bikerglen/usb-knob-box-bmd-remote/pic18/software/USB-Knobs-v02.X/system.c

/*******************************************************************************
Copyright 2016 Microchip Technology Inc. (www.microchip.com)

Licensed under the Apache License, Version 2.0 (the "License");
you may not use this file except in compliance with the License.
You may obtain a copy of the License at

    http://www.apache.org/licenses/LICENSE-2.0

Unless required by applicable law or agreed to in writing, software
distributed under the License is distributed on an "AS IS" BASIS,
WITHOUT WARRANTIES OR CONDITIONS OF ANY KIND, either express or implied.
See the License for the specific language governing permissions and
limitations under the License.

To request to license the code under the MLA license (www.microchip.com/mla_license), 
please contact mla_licensing@microchip.com
*******************************************************************************/

#include <xc.h>
#include "system.h"
#include "usb.h"

/** CONFIGURATION Bits **********************************************/
#pragma config PLLSEL   = PLL3X     // PLL Selection (3x clock multiplier)
#pragma config CFGPLLEN = OFF       // PLL Enable Configuration bit (PLL Disabled (firmware controlled))
#pragma config CPUDIV   = NOCLKDIV  // CPU System Clock Postscaler (CPU uses system clock (no divide))
#pragma config LS48MHZ  = SYS48X8   // Low Speed USB mode with 48 MHz system clock (System clock at 48 MHz, USB clock divider is set to 8)
#pragma config FOSC     = INTOSCIO  // Oscillator Selection (Internal oscillator)
#pragma config PCLKEN   = OFF       // Primary Oscillator Shutdown (Primary oscillator shutdown firmware controlled)
#pragma config FCMEN    = OFF       // Fail-Safe Clock Monitor (Fail-Safe Clock Monitor disabled)
#pragma config IESO     = OFF       // Internal/External Oscillator Switchover (Oscillator Switchover mode disabled)
#pragma config nPWRTEN  = OFF       // Power-up Timer Enable (Power up timer disabled)
#pragma config BOREN    = SBORDIS   // Brown-out Reset Enable (BOR enabled in hardware (SBOREN is ignored))
#pragma config BORV     = 190       // Brown-out Reset Voltage (BOR set to 1.9V nominal)
#pragma config nLPBOR   = ON        // Low-Power Brown-out Reset (Low-Power Brown-out Reset enabled)
#pragma config WDTEN    = SWON      // Watchdog Timer Enable bits (WDT controlled by firmware (SWDTEN enabled))
#pragma config WDTPS    = 32768     // Watchdog Timer Postscaler (1:32768)
#pragma config CCP2MX   = RC1       // CCP2 MUX bit (CCP2 input/output is multiplexed with RC1)
#pragma config PBADEN   = OFF       // PORTB A/D Enable bit (PORTB<5:0> pins are configured as digital I/O on Reset)
#pragma config T3CMX    = RC0       // Timer3 Clock Input MUX bit (T3CKI function is on RC0)
#pragma config SDOMX    = RC7       // SDO Output MUX bit (SDO function is on RC7)
#pragma config MCLRE    = ON        // Master Clear Reset Pin Enable (MCLR pin enabled; RE3 input disabled)
#pragma config STVREN   = ON        // Stack Full/Underflow Reset (Stack full/underflow will cause Reset)
#pragma config LVP      = OFF       // Single-Supply ICSP Enable bit (Single-Supply ICSP disabled)
#pragma config ICPRT    = OFF       // Dedicated In-Circuit Debug/Programming Port Enable (ICPORT disabled)
#pragma config XINST    = OFF       // Extended Instruction Set Enable bit (Instruction set extension and Indexed Addressing mode disabled)
#pragma config CP0      = OFF       // Block 0 Code Protect (Block 0 is not code-protected)
#pragma config CP1      = OFF       // Block 1 Code Protect (Block 1 is not code-protected)
#pragma config CP2      = OFF       // Block 2 Code Protect (Block 2 is not code-protected)
#pragma config CP3      = OFF       // Block 3 Code Protect (Block 3 is not code-protected)
#pragma config CPB      = OFF       // Boot Block Code Protect (Boot block is not code-protected)
#pragma config CPD      = OFF       // Data EEPROM Code Protect (Data EEPROM is not code-protected)
#pragma config WRT0     = OFF       // Block 0 Write Protect (Block 0 (0800-1FFFh) is not write-protected)
#pragma config WRT1     = OFF       // Block 1 Write Protect (Block 1 (2000-3FFFh) is not write-protected)
#pragma config WRT2     = OFF       // Block 2 Write Protect (Block 2 (04000-5FFFh) is not write-protected)
#pragma config WRT3     = OFF       // Block 3 Write Protect (Block 3 (06000-7FFFh) is not write-protected)
#pragma config WRTC     = OFF       // Configuration Registers Write Protect (Configuration registers (300000-3000FFh) are not write-protected)
#pragma config WRTB     = OFF       // Boot Block Write Protect (Boot block (0000-7FFh) is not write-protected)
#pragma config WRTD     = OFF       // Data EEPROM Write Protect (Data EEPROM is not write-protected)
#pragma config EBTR0    = OFF       // Block 0 Table Read Protect (Block 0 is not protected from table reads executed in other blocks)
#pragma config EBTR1    = OFF       // Block 1 Table Read Protect (Block 1 is not protected from table reads executed in other blocks)
#pragma config EBTR2    = OFF       // Block 2 Table Read Protect (Block 2 is not protected from table reads executed in other blocks)
#pragma config EBTR3    = OFF       // Block 3 Table Read Protect (Block 3 is not protected from table reads executed in other blocks)
#pragma config EBTRB    = OFF       // Boot Block Table Read Protect (Boot block is not protected from table reads executed in other blocks)


// S.BUS data
extern volatile uint8_t txByte;
extern volatile uint8_t sbusData[25];

// S>BUS data IRQ parity calculation variables
static uint8_t x, y;


void SYSTEM_Initialize( SYSTEM_STATE state )
{
    switch(state)
    {
        case SYSTEM_STATE_USB_START:
		
            //Configure oscillator settings for clock settings compatible with USB
            //operation.  Note: Proper settings depends on USB speed (full or low).
            #if(USB_SPEED_OPTION == USB_FULL_SPEED)
                OSCTUNE = 0x80; //3X PLL ratio mode selected
                OSCCON = 0x70;  //Switch to 16MHz HFINTOSC
                OSCCON2 = 0x10; //Enable PLL, SOSC, PRI OSC drivers turned off
                while(OSCCON2bits.PLLRDY != 1);   //Wait for PLL lock
                ACTCON = 0x90;  //Enable active clock tuning for USB operation
            #endif
			
            break;
            
        case SYSTEM_STATE_USB_SUSPEND:
            break;
            
        case SYSTEM_STATE_USB_RESUME:
            break;
    }
}


void __interrupt(high_priority) SYS_InterruptHigh(void)
{
    #if defined(USB_INTERRUPT)
        USBDeviceTasks();
    #endif
}


void __interrupt(low_priority) SYS_InterruptLow(void)
{
#if 0    
    if (INTCONbits.TMR0IE == 1 && INTCONbits.TMR0IF == 1)
    {
        TMR0_InterruptHandler();
    }
#endif
    
    if (INTCONbits.TMR0IE == 1 && INTCONbits.TMR0IF == 1)
    {
        TMR0H = TMR0_RELOAD_VALUE >> 8;
        TMR0L = TMR0_RELOAD_VALUE & 0xFF;
        INTCONbits.TMR0IF = 0;
        
        x = sbusData[txByte++];
        y = x ^ (x >> 4);
        y = y ^ (y >> 2);
        y = y ^ (y >> 1);
        TXSTA1bits.TX9D = y & 1;
        TXREG1 = x;

        if (txByte >= 25) {
            INTCONbits.TMR0IE = 0;
        }
    }
    
    if (PIE1bits.TMR2IE == 1 && PIR1bits.TMR2IF == 1)
    {
        TMR2_InterruptHandler();
    }

/*                
    if (PIE1bits.TX1IE == 1 && PIR1bits.TX1IF == 1) 
    {
        x = sbusData[txByte++];
        y = x ^ (x >> 4);
        y = y ^ (y >> 2);
        y = y ^ (y >> 1);
        TXSTA1bits.TX9D = y & 1;
        TXREG1 = x;
        if (txByte >= 25) {
            PIE1bits.TX1IE = 0;
        }
    }
*/
}
