bikerglen/usb-knob-box-bmd-remote/efm8ub2/software/EFM8UB2_HID_VendorDefined_Knobs_01/src/callback.c

/**************************************************************************//**
 * Copyright (c) 2015 by Silicon Laboratories Inc. All rights reserved.
 *
 * http://developer.silabs.com/legal/version/v11/Silicon_Labs_Software_License_Agreement.txt
 *****************************************************************************/

#include "SI_EFM8UB2_Register_Enums.h"
#include "efm8_usb.h"
#include "descriptors.h"
#include "idle.h"
#include "config.h"

uint8_t tmpBuffer;
uint8_t xdata txBuffer[64];
uint8_t xdata rxBuffer[64];

extern volatile uint8_t xdata usbReportNeeded;
extern volatile uint8_t xdata usbReportData[6];

SI_SBIT(SW1_LED,  SFR_P2, 3); // SW1 LED -- top button on top of board
SI_SBIT(SW2_LED,  SFR_P2, 2); // SW2 LED -- bottom button on top of board
SI_SBIT(USER_LED, SFR_P0, 6); // USER LED -- on bottom of board

#define LED_ON  0
#define LED_OFF 1


// ----------------------------------------------------------------------------
// Functions
// ----------------------------------------------------------------------------
void USBD_ResetCb(void)
{

}

void USBD_SofCb(uint16_t sofNr)
{
	UNREFERENCED_ARGUMENT(sofNr);

	idleTimerTick();

	// Check if the device should send a report
	if (isIdleTimerExpired() == true)
	{
	    if (USBD_EpIsBusy(EP1IN) == false) {
	    	if (usbReportNeeded) {
	    		usbReportNeeded = false;
			    txBuffer[0] = 0x01;
  			    txBuffer[1] = usbReportData[0];
  			    txBuffer[2] = usbReportData[1];
  			    txBuffer[3] = usbReportData[2];
  			    txBuffer[4] = usbReportData[3];
  			    txBuffer[5] = usbReportData[4];
  			    txBuffer[6] = usbReportData[5];
				USBD_Write (EP1IN, txBuffer, 7, false);
	    	}
	    }
	}
}

void USBD_DeviceStateChangeCb(USBD_State_TypeDef oldState,
                              USBD_State_TypeDef newState)
{
  // If not configured or in suspend, disable the LED
  if (newState < USBD_STATE_SUSPENDED)
  {
  }
  // Entering suspend mode, power internal and external blocks down
  else if (newState == USBD_STATE_SUSPENDED)
  {
    // Abort any pending transfer
    USBD_AbortTransfer(EP1IN);
  }
  else if (newState == USBD_STATE_CONFIGURED)
  {
	    idleTimerSet(POLL_RATE);
		USBD_Read (EP1OUT, rxBuffer, 16, true);
  }

  // Exiting suspend mode, power internal and external blocks up
  if (oldState == USBD_STATE_SUSPENDED)
  {
  }
}

bool USBD_IsSelfPoweredCb(void)
{
  return true;
}

USB_Status_TypeDef USBD_SetupCmdCb(SI_VARIABLE_SEGMENT_POINTER(
                                     setup,
                                     USB_Setup_TypeDef,
                                     MEM_MODEL_SEG))
{
  USB_Status_TypeDef retVal = USB_STATUS_REQ_UNHANDLED;

  if ((setup->bmRequestType.Type == USB_SETUP_TYPE_STANDARD)
      && (setup->bmRequestType.Direction == USB_SETUP_DIR_IN)
      && (setup->bmRequestType.Recipient == USB_SETUP_RECIPIENT_INTERFACE))
  {
    // A HID device must extend the standard GET_DESCRIPTOR command
    // with support for HID descriptors.
    switch (setup->bRequest)
    {
      case GET_DESCRIPTOR:
        if ((setup->wValue >> 8) == USB_HID_REPORT_DESCRIPTOR)
        {
          switch (setup->wIndex)
          {
            case 0: // Interface 0

              USBD_Write(EP0,
                         (SI_VARIABLE_SEGMENT_POINTER(, uint8_t, SI_SEG_GENERIC))ReportDescriptor0,
                         EFM8_MIN(sizeof(ReportDescriptor0), setup->wLength),
                         false);
              retVal = USB_STATUS_OK;
              break;

            default: // Unhandled Interface
              break;
          }
        }
        else if ((setup->wValue >> 8) == USB_HID_DESCRIPTOR)
        {
          switch (setup->wIndex)
          {
            case 0: // Interface 0

              USBD_Write(EP0,
                         (SI_VARIABLE_SEGMENT_POINTER(, uint8_t, SI_SEG_GENERIC))(&configDesc[18]),
                         EFM8_MIN(USB_HID_DESCSIZE, setup->wLength),
                         false);
              retVal = USB_STATUS_OK;
              break;

            default: // Unhandled Interface
              break;
          }
        }
        break;
    }
  }
  else if ((setup->bmRequestType.Type == USB_SETUP_TYPE_CLASS)
           && (setup->bmRequestType.Recipient == USB_SETUP_RECIPIENT_INTERFACE)
           && (setup->wIndex == HID_VENDOR_IFC))
  {
    // Implement the necessary HID class specific commands.
    switch (setup->bRequest)
    {
      case USB_HID_SET_IDLE:
        if (((setup->wValue & 0xFF) == 0)             // Report ID
            && (setup->wLength == 0)
            && (setup->bmRequestType.Direction != USB_SETUP_DIR_IN))
        {
          idleTimerSet(setup->wValue >> 8);
          retVal = USB_STATUS_OK;
        }
        break;

      case USB_HID_GET_IDLE:
        if ((setup->wValue == 0)                      // Report ID
            && (setup->wLength == 1)
            && (setup->bmRequestType.Direction == USB_SETUP_DIR_IN))
        {
          tmpBuffer = idleGetRate();
          USBD_Write(EP0, &tmpBuffer, 1, false);
          retVal = USB_STATUS_OK;
        }
        break;
    }
  }

  return retVal;
}

uint16_t USBD_XferCompleteCb(uint8_t epAddr,
                             USB_Status_TypeDef status,
                             uint16_t xferred,
                             uint16_t remaining)
{
	UNREFERENCED_ARGUMENT(status);
	UNREFERENCED_ARGUMENT(xferred);
	UNREFERENCED_ARGUMENT(remaining);

	if (epAddr == EP1OUT) {
		if (rxBuffer[0] == 0x02) {
			if (rxBuffer[1] & 0x01) SW1_LED = LED_ON; else SW1_LED = LED_OFF;
			if (rxBuffer[1] & 0x02) SW2_LED = LED_ON; else SW2_LED = LED_OFF;
		}
		USBD_Read (EP1OUT, rxBuffer, 16, true);
	}

	return 0;
}
