bikerglen/usb-knob-box-bmd-remote/pic18/software/USB-Knobs-v02.X/app_device_custom_hid.c

/*******************************************************************************
Copyright 2016 Microchip Technology Inc. (www.microchip.com)

Licensed under the Apache License, Version 2.0 (the "License");
you may not use this file except in compliance with the License.
You may obtain a copy of the License at

    http://www.apache.org/licenses/LICENSE-2.0

Unless required by applicable law or agreed to in writing, software
distributed under the License is distributed on an "AS IS" BASIS,
WITHOUT WARRANTIES OR CONDITIONS OF ANY KIND, either express or implied.
See the License for the specific language governing permissions and
limitations under the License.

To request to license the code under the MLA license (www.microchip.com/mla_license), 
please contact mla_licensing@microchip.com
*******************************************************************************/

/** INCLUDES *******************************************************/
#include "usb.h"
#include "usb_device_hid.h"

#include <string.h>

#include "system.h"


/** VARIABLES ******************************************************/
/* Some processors have a limited range of RAM addresses where the USB module
 * is able to access.  The following section is for those devices.  This section
 * assigns the buffers that need to be used by the USB module into those
 * specific areas.
 */
#if defined(FIXED_ADDRESS_MEMORY)
    #if defined(COMPILER_MPLAB_C18)
        #pragma udata HID_CUSTOM_OUT_DATA_BUFFER = HID_CUSTOM_OUT_DATA_BUFFER_ADDRESS
        unsigned char ReceivedDataBuffer[64];
        #pragma udata HID_CUSTOM_IN_DATA_BUFFER = HID_CUSTOM_IN_DATA_BUFFER_ADDRESS
        unsigned char ToSendDataBuffer[64];
        #pragma udata

    #elif defined(__XC8)
        unsigned char ReceivedDataBuffer[64] HID_CUSTOM_OUT_DATA_BUFFER_ADDRESS;
        unsigned char ToSendDataBuffer[64] HID_CUSTOM_IN_DATA_BUFFER_ADDRESS;
    #endif
#else
    unsigned char ReceivedDataBuffer[64];
    unsigned char ToSendDataBuffer[64];
#endif

volatile USB_HANDLE USBOutHandle;    
volatile USB_HANDLE USBInHandle;

extern volatile uint8_t usbReportNeeded;
extern volatile uint8_t usbReportData[6];

/** DEFINITIONS ****************************************************/

/** FUNCTIONS ******************************************************/

/*********************************************************************
* Function: void APP_DeviceCustomHIDInitialize(void);
*
* Overview: Initializes the Custom HID demo code
*
* PreCondition: None
*
* Input: None
*
* Output: None
*
********************************************************************/
void APP_DeviceCustomHIDInitialize()
{
    //initialize the variable holding the handle for the last
    // transmission
    USBInHandle = 0;

    //enable the HID endpoint
    USBEnableEndpoint(CUSTOM_DEVICE_HID_EP, USB_IN_ENABLED|USB_OUT_ENABLED|USB_HANDSHAKE_ENABLED|USB_DISALLOW_SETUP);

    //Re-arm the OUT endpoint for the next packet
    USBOutHandle = (volatile USB_HANDLE)HIDRxPacket(CUSTOM_DEVICE_HID_EP,(uint8_t*)&ReceivedDataBuffer[0],64);
}

/*********************************************************************
* Function: void APP_DeviceCustomHIDTasks(void);
*
* Overview: Keeps the Custom HID demo running.
*
* PreCondition: The demo should have been initialized and started via
*   the APP_DeviceCustomHIDInitialize() and APP_DeviceCustomHIDStart() demos
*   respectively.
*
* Input: None
*
* Output: None
*
********************************************************************/
void APP_DeviceCustomHIDTasks()
{   
    /* If the USB device isn't configured yet, we can't really do anything
     * else since we don't have a host to talk to.  So jump back to the
     * top of the while loop. */
    if( USBGetDeviceState() < CONFIGURED_STATE )
    {
        return;
    }

    /* If we are currently suspended, then we need to see if we need to
     * issue a remote wakeup.  In either case, we shouldn't process any
     * keyboard commands since we aren't currently communicating to the host
     * thus just continue back to the start of the while loop. */
    if( USBIsDeviceSuspended()== true )
    {
        return;
    }
    
    //Check if we have received an OUT data packet from the host
    if(HIDRxHandleBusy(USBOutHandle) == false)
    {   
        // check report ID
        if (ReceivedDataBuffer[0] == 2) {
            if (ReceivedDataBuffer[1] & 1) {
                SW1_LED = LED_ON;
            } else {
                SW1_LED = LED_OFF;
            }
            if (ReceivedDataBuffer[1] & 2) {
                SW2_LED = LED_ON;
            } else {
                SW2_LED = LED_OFF;
            }
        }
        
        //Re-arm the OUT endpoint, so we can receive the next OUT data packet 
        //that the host may try to send us.
        USBOutHandle = HIDRxPacket(CUSTOM_DEVICE_HID_EP, (uint8_t*)&ReceivedDataBuffer[0], 64);
    }
    
    if (usbReportNeeded) {
        if (!HIDTxHandleBusy(USBInHandle)) {
            usbReportNeeded = false;
            ToSendDataBuffer[0] = 0x01; // report ID
            ToSendDataBuffer[1] = usbReportData[0];
            ToSendDataBuffer[2] = usbReportData[1];
            ToSendDataBuffer[3] = usbReportData[2];
            ToSendDataBuffer[4] = usbReportData[3];
            ToSendDataBuffer[5] = usbReportData[4];
            ToSendDataBuffer[6] = usbReportData[5];
            //Prepare the USB module to send the data packet to the host
            USBInHandle = HIDTxPacket(CUSTOM_DEVICE_HID_EP, (uint8_t*)&ToSendDataBuffer[0],7);
        }
    }
}
